andykarpov/radio-86rk-sdcard/firmware/src/atmega328p/common.h

// SD Controller for Computer "Radio 86RK" / "Apogee BK01"
// (c) 10-05-2014 vinxru (aleksey.f.morozov@gmail.com)

#ifndef COMMON_H
#define COMMON_H

#include <mega328p.h>

#define CONST

typedef unsigned char   BYTE;
typedef unsigned short  WORD;
typedef unsigned long	DWORD;

#endif
