andykarpov/radio-86rk-sdcard/firmware/src/avrgcc-playground/proto.h

// SD Controller for Computer "Radio 86RK" / "Apogee BK01"
// (c) 10-05-2014 vinxru (aleksey.f.morozov@gmail.com)

#include "common.h"

#define DATA_OUT    DDRD = 0b11111111;
#define DATA_IN     DDRD = 0b00000000;

void wait(void);
void sendStart(uint8_t c); 
void send(uint8_t c);
void recvStart(void);
uint8_t wrecv(void);
